Bastardkb/Scylla/pics/1.jpg

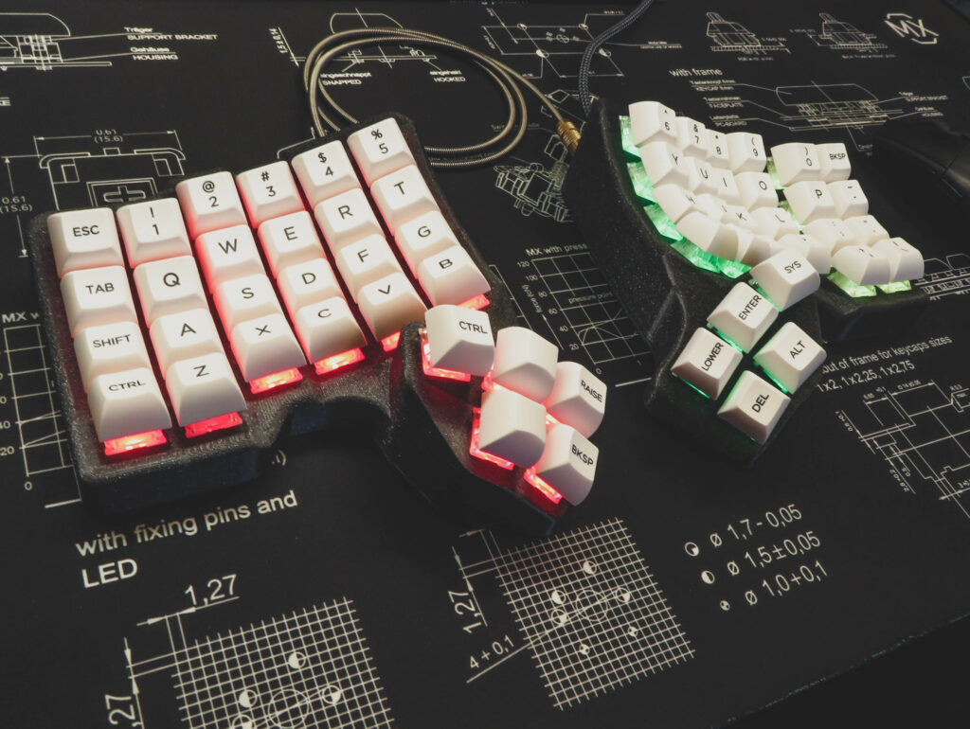
pics/1.jpg
